H3wastooshort/usbc2dell/firmware/src/emu_controller.hpp

#pragma once
#include <PD_UFP.h>
#include "chg_emu.hpp"

enum negotiantion_states_e
{
    NEG_INIT = 0,
    NEG_WAIT_FOR_PD_TRANS,
    NEG_WAIT_FOR_PD,
    NEG_GOT_20V_TRANS,
    NEG_GOT_20V,
    NEG_GOT_PPS_TRANS,
    NEG_GOT_PPS,
};

class EmuController {
    //not copyable
    EmuController(const EmuController&) = delete;
    EmuController& operator=(const EmuController&) = delete;
    
    const bool use_pps;

    chg_emu_c *emulator;
    PD_UFP_c pd;
    TwoWire *i2c;

    negotiantion_states_e negotiantion_state;

    void sm_run();
    void sm_change_state(const negotiantion_states_e new_state);
    
    public:
    EmuController(TwoWire* i2c, const bool use_pps, chg_emu_c *emulator);
    void setup();
    void loop();
};
