H3wastooshort/usbc2dell/firmware/src/chg_emu.hpp

#pragma once
#include <Arduino.h>
class chg_emu_c {
protected:
    ~chg_emu_c() = default;
public:
    virtual void setup() = 0;
    virtual void loop() = 0;
    virtual void set_param(uint32_t millivolt, uint32_t milliamp) = 0;
    virtual void enable() = 0;
    virtual void disable() = 0;
};
